Carciax/EEE3088F-Project-CKR/Temp/EEE3088F_CKR.csv

Reference | Value | Footprint | Datasheet | DNF | Extended Part Cost | JLC code | Part name | Sim.Enable | cost per unit | Qty
C1-C4 | 10uf | footprint:C0603 | ~ |  | 0 | -- mixed values -- | CL10A106KP8NNNC |  | 0,0066 | 4
C5 | 100n | footprint:C0402_NEW | ~ |  | 0 | C1525 | CL05B104KO5NNNC |  | 0.0011 | 1
C6 | 1u | footprint:C0402 | ~ |  | 0 | C52923 | CL05A105KA5NQNC |  | 0,0039 | 1
D1 | zener diode | footprint:SOD-123_L2.8-W1.8-LS3.7-RD |  |  | 3 | C36599 | MMSZ4678T18 |  | 0,0956 | 1
D2 | LED Green | footprint:LED0805-R-RD | ~ |  | 0 | C2296 | 17-21SUYC/TR8 |  | 0,0119 | 1
D3 | LED RED | footprint:LED0603-RD | ~ |  | 0 | C2286 | LED_0603 |  | 0,0054 | 1
D4, D5 | LED | footprint:LED0603-RD | ~ |  | 0 | C2286 | LED_0603 |  | 0,0054 | 2
J1, J2 | Conn_01x02_Pin | footprint:HDR-TH_2P-P2.54-V-M | ~ | X | 0 | C5116481 | 2.54-1*2 |  | 0 | 2
J3 |  | footprint:STM32F051C6_female_header |  |  | 0 | C2883741 | X6511FV-24-C85D32 |  | 0 | 1
J4 | STM32F051C6_testpoints |  |  |  |  |  |  |  |  | 1
J5 | Debugger | footprint:HDR-TH_3P-P2.54_CS-1165SDIG | ~ |  | 0 | C2886705 | CS-1165SDIG-1*3 |  | 0 | 1
J6 | Conn_01x10_Pin |  | ~ |  |  |  |  |  |  | 1
JP1-JP6 | Jumper_2_Bridged |  | ~ |  |  |  |  |  |  | 6
JP7, JP8 | Jumper_3_Bridged12 |  | ~ |  |  |  |  |  |  | 2
Q1-Q8 | AO3401A | footprint:SOT-23_L2.9-W1.3-P1.90-LS2.4-BR | http://www.aosmd.com/pdfs/datasheet/AO3401A.pdf |  | 0 | C15127 | AO3401A |  | 0,0797 | 8
R1 | 1M | footprint:R0603 | ~ |  | 0 | C23156 | 0603WAF3004T5E |  | 0,0013 | 1
R2, R3, R5, R11, R16, R17, R19-R22, R24-R28, R30-R33, R36-R46, R48-R51, R57-R63 | 0 | footprint:R0603 | ~ |  | 0 | C21189 | 0603WAF0000T5E | -- mixed values -- | 0,0010 | 41
R4, R10, R12, R15, R18, R23, R34, R35 | 1.2k | footprint:R0805 | ~ |  | 0 | C17630 | 0805W8F3300T5E |  | 0,0016 | 8
R6, R13 | R1M | footprint:R0805 | ~ |  | 0 | C17514 | 0805W8F1004T5E |  | 0,0016 | 2
R7 | R2M | footprint:R0805 | ~ |  | 0 | C26112 | 0805W8F2004T5E |  | 0,0024 | 1
R8 | 27.5k | footprint:R0805 | ~ |  | 0 | C17593 | 0805W8F2702T5E |  | 0,0018 | 1
R9, R47 | 10k | footprint:R0805 | ~ |  | 0 | C17414 | 0805W8F1002T5E |  | 0,0010 | 2
R14 | R3M | footprint:R0603 | ~ |  | 0 | C23156 | 0603WAF3004T5E |  | 0,0013 | 1
R29 | 100k | footprint:R1206 | ~ |  | 0 | C17900 | 1206W4F1003T5E |  | 0,0031 | 1
R52-R55 | 3.9k | footprint:R0402 | ~ |  | 0 | C51721 | 0402WGF3901TCE |  | 0,0006 | 4
R56 | 8.2k | footprint:R0402 | ~ |  | 0 | C25924 | 0402WGF8201TCE |  | 0,0005 | 1
R64 | R1M | footprint:R0603 | ~ |  | 0 | C23156 | 0603WAF3004T5E |  | 0,0013 | 1
R65 | R2M | footprint:R0603 | ~ |  | 0 | C23156 | 0603WAF3004T5E |  | 0,0013 | 1
RV1 | R_Potentiometer | footprint:RES-ADJ-TH_RK09K1130AJ3 | ~ |  | 3 | C388854 | RK09K1130AJ3 |  | 0,5956 | 1
SW1 | Reset switch | footprint:SW-SMD_4P-L5.1-W5.1-P3.70-LS6.5-TL-2 | ~ |  | 0 | C318884 | TS-1187A-B-A-B |  | 0,0152 | 1
SW2-SW4 | switch | footprint:SW-SMD_4P-L5.1-W5.1-P3.70-LS6.5-TL-2 | ~ |  | 0 | C318884 | TS-1187A-B-A-B |  | 0,0152 | 3
TH1 | Thermistor | footprint:R0402 | ~ |  | 3 | C77130 | NCP15WF104F03RC |  | 0.0130 | 1
TP1 | 5v | footprint:Testpoint_2.54mm | ~ |  | 0 |  |  |  | 0 | 1
TP2 | UVLO | footprint:Testpoint_2.54mm | ~ |  | 0 |  |  |  | 0 | 1
TP3 | battery charger | footprint:Testpoint_2.54mm | ~ |  | 0 |  |  |  | 0 | 1
TP4, TP6 | reverse polarity | footprint:Testpoint_2.54mm | ~ |  | 0 |  |  |  | 0 | 2
TP5 | 3.3v out | footprint:Testpoint_2.54mm | ~ |  | 0 |  |  |  | 0 | 1
TP7 | Pot ADC | footprint:Testpoint_2.54mm | ~ |  | 0 |  |  |  | 0 | 1
TP8 | Therm ADC | footprint:Testpoint_2.54mm | ~ |  | 0 |  |  |  | 0 | 1
TP9 | Sensors SDA | footprint:Testpoint_2.54mm | ~ |  | 0 |  |  |  | 0 | 1
TP10 | Sensors SCL | footprint:Testpoint_2.54mm | ~ |  | 0 |  |  |  | 0 | 1
TP11 | Light Interrupt | footprint:Testpoint_2.54mm | ~ |  | 0 |  |  |  | 0 | 1
TP12 | STM32 LED1 | footprint:Testpoint_2.54mm | ~ |  | 0 |  |  |  | 0 | 1
TP13 | STM32 LED2 | footprint:Testpoint_2.54mm | ~ |  | 0 |  |  |  | 0 | 1
TP14 | NSRT | footprint:Testpoint_2.54mm | ~ |  | 0 |  |  |  | 0 | 1
TP15 | Switch1 | footprint:Testpoint_2.54mm | ~ |  | 0 |  |  |  | 0 | 1
TP16 | Switch2 | footprint:Testpoint_2.54mm | ~ |  | 0 |  |  |  | 0 | 1
TP17 | Switch3 | footprint:Testpoint_2.54mm | ~ |  | 0 |  |  |  | 0 | 1
TP18 | STM32 3V3 | footprint:Testpoint_2.54mm | ~ |  | 0 |  |  |  | 0 | 1
TP19 | STM32 GND | footprint:Testpoint_2.54mm | ~ |  | 0 |  |  |  | 0 | 1
TP20 | STM32 Tx | footprint:Testpoint_2.54mm | ~ |  | 0 |  |  |  | 0 | 1
TP21 | STM32 Rx | footprint:Testpoint_2.54mm | ~ |  | 0 |  |  |  | 0 | 1
TP22 | EEPROM SDA | footprint:Testpoint_2.54mm | ~ |  | 0 |  |  |  | 0 | 1
TP23 | EEPROM SCL | footprint:Testpoint_2.54mm | ~ |  | 0 |  |  |  | 0 | 1
TP24 | USB D- | footprint:Testpoint_2.54mm | ~ |  | 0 |  |  |  | 0 | 1
TP25 | USB D+ | footprint:Testpoint_2.54mm | ~ |  | 0 |  |  |  | 0 | 1
U1 | LMV321 | footprint:SOT-23-5_L3.0-W1.7-P0.95-LS2.8-BR | http://www.ti.com/lit/ds/symlink/lmv324.pdf |  | 0 | C7972 | LMV321 |  | 0,1439 | 1
U2 | Battery Charger | footprint:ESOP-8_L4.9-W3.9-P1.27-LS6.0-BL-EP |  |  | 0 | C16581 | TP4056 |  | 0,2064 | 1
u3 | battery holder | footprint:BATTERY-SMD_18650-1S-L77.1-W20.7-1 | ~ | x | 0 | C2988620 | BH-18650-B1BA002 |  | 0 | 1
U4 | XC6206PxxxMR | footprint:SOT-23-3_L2.9-W1.6-P1.90-LS2.8-BR | https://www.torexsemi.com/file/xc6206/XC6206.pdf |  | 0 | C5446 | XC6206P332MR |  | 0,0964 | 1
U5 | GXHTC3 | footprint:DFN-6_L2.0-W2.0-P0.50-BL-EP |  |  | 3 | C2837688 | GXHTC3 |  | 0,8714 | 1
U6 | LTR-303ALS-01 | footprint:SOT-363_L2.0-W1.3-P0.65-LS2.1-BL | http://optoelectronics.liteon.com/upload/download/DS86-2013-0004/LTR-303ALS-01_DS_V1.pdf |  | 3 | C364577 | LTR-303ALS-01 |  | 0,3762 | 1
U7 | 24LC256 | footprint:PDIP-8_L9.3-W6.4-P2.54-LS7.6-BL | http://ww1.microchip.com/downloads/en/devicedoc/21203m.pdf |  | 3 | C411624 | 24LC256 |  | 1.6033 | 1
U8 | usb | footprint:MICRO-USB-SMD_MICROXNJ |  |  | 3 | C404969 | MicroXNJ |  | 0.0333 | 1
U9 | HT42B534-2 | footprint:SOIC-8_L4.9-W3.9-P1.27-LS6.0-BL |  |  | 3 | C493294 | HT42B534-2 |  | 0.7554 | 1
