Carciax/EEE3088F-Project-CKR/Documentation/3.1.xlsx

Parks required | name of component being used | Maximum and minimum input voltage |  | output voltage | Current required | temp max | other requirements | data sheet
mandatory USB connection | C404969 |  |  |  |  | -20℃~+85℃
Lytham ion battery |  |  |  | 3.3 volts |  |  | will see what current is requeerd
lithium ion battery charger |  | 0.3 | 8 |  |  | 85°C |  | https://pdf1.alldatasheet.com/datasheet-pdf/view/1487471/ETC2/TP4056.html
red LED
Green LED
10 uf capitor
Under voltage lockout
voltag reulater and ulvo | https://jlcpcb.com/partdetail/DiodesIncorporated-AP7365_33WG7/C150742
 | https://jlcpcb.com/parts/componentSearch?searchTxt=LM2937
