Carciax/EEE3088F-Project-CKR/Code/Core/Src/light.h

//Slave addresses
#define LIGHT_ADDR = (0x29)
#define LIGHT_ADDR_16L (0x29 << 9)
#define LIGHT_ADDR_WRITE = (0x52)
#define LIGHT_ADDR_READ = (0x53)

//Control
#define LIGHT_CONTR = (0x80)
#define LIGHT_CONTR_SIZE = (8)
#define LIGHT_CONTR_ACTIVE = (0b00000001)
#define LIGHT_CONTR_STARTUP = (0b00000010)
